Omnisens-iot/Estrategia-y-Gesti-n-de-Proyectos-para-Soluciones-IoT-/B_Investigacion/Gestion_de_proyectos/9. Crear matriz inicial de riesgos del proyecto.docx.pdf

## 9. Crear matriz inicial de riesgos del proyecto

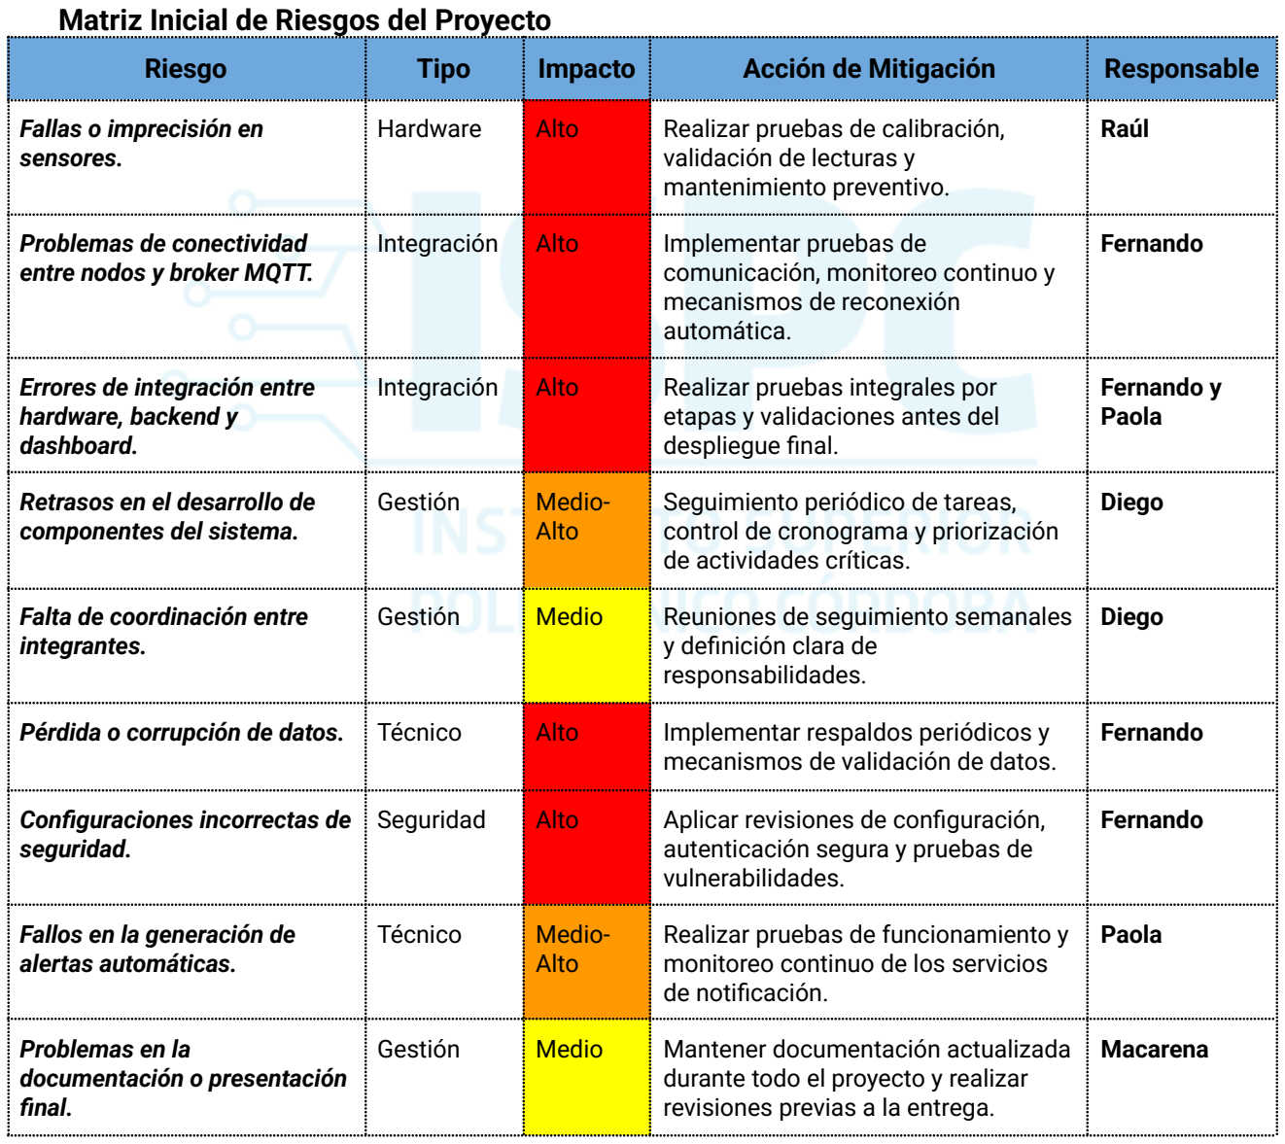
[picture p5: figure]
Matriz Inicial de Riesgos del Proyecto; Riesgo; Tipo; Impacto; Acción de Mitigación; Responsable; Fallas o imprecisión en sensores.; Hardware; Alto; Realizar pruebas de calibración,; validación de lecturas y mantenimiento preventivo.; Raúl; Problemas de conectividad entre nodos y broker MQTT.; Integración; Implementar pruebas de; comunicación, monitoreo continuo y mecanismos de reconexión automática.; Fernando; Errores de integración entre hardware, backend y dashboard.; Realizar pruebas integrales por; etapas y validaciones antes del despliegue final.; Fernando y Paola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

Pérdida o corrupción de datos. Técnico | Alto | Implementar respaldos periódicos y

### Resultado esperado

La matriz de riesgos permite identificar tempranamente posibles problemas técnicos y de gestión asociados al desarrollo de OmniSens. La asignación de responsables y acciones de mitigación facilita el seguimiento continuo de los riesgos y contribuye al cumplimiento de los objetivos del proyecto.
