Omnisens-iot/Estrategia-y-Gesti-n-de-Proyectos-para-Soluciones-IoT-/B_Investigacion/Modelo_negocios/6.1 Definir beneficios del sistema para el cliente.docx.pdf

### 6.1 Definir beneficios del sistema para el cliente

### 1. Mayor seguridad operativa

OmniSens permite monitorear variables ambientales críticas en tiempo real, facilitando la detección temprana de condiciones anómalas y mejorando la capacidad de respuesta ante posibles incidentes.

### 2. Reducción de riesgos

La generación automática de alertas y la supervisión continua ayudan a prevenir fallas operativas, minimizar interrupciones en los procesos y reducir la probabilidad de eventos que afecten la seguridad de las instalaciones.

### 3. Optimización de recursos

Al centralizar la información y automatizar tareas de monitoreo, se reducen los controles manuales, se mejora la eficiencia operativa y se facilita la toma de decisiones basada en datos confiables.

### 4. Cumplimiento normativo

El almacenamiento histórico de datos y la trazabilidad de la información permiten generar evidencias y reportes que contribuyen al cumplimiento de normativas de seguridad, higiene y control ambiental.

Resultado Final
OmniSens brinda a las organizaciones una herramienta que mejora la seguridad operativa, reduce riesgos, optimiza recursos y facilita el cumplimiento normativo, transformando datos ambientales en información útil para la toma de decisiones preventivas.
