Omnisens-iot/Estrategia-y-Gesti-n-de-Proyectos-para-Soluciones-IoT-/B_Investigacion/Gestion_de_proyectos/6. Definir roles y responsabilidades de los 5 integrantes.docx.pdf

6. Definir roles y responsabilidades de los 5 integrantes.
Integrante | Rol | Responsabilidades
Diego | Coordinador del Proyecto | Planificación y seguimiento de actividades, coordinación del equipo, control de cronograma, gestión de riesgos y supervisión general de los entregables.
Raúl | Responsable de Hardware y Firmware | Integración de sensores y nodos ESP32, desarrollo y mantenimiento del firmware, pruebas de funcionamiento y validación de la adquisición de datos.
Fernando | Responsable de Backend e Infraestructura | Configuración del broker MQTT, desarrollo de servicios backend, gestión de bases de datos, infraestructura cloud (AWS EC2), Docker y automatización de despliegues.
Paola | Responsable de Datos y Visualización | Diseño y desarrollo del dashboard, visualización de datos en tiempo real, configuración de alertas, reportes y validación de la calidad de los datos.
Macarena | Responsable de Documentación y Presentación | Elaboración de documentación técnica y funcional, actualización del repositorio, preparación de presentaciones, informes, defensa del proyecto y consolidación de entregables.

Resultado esperado

La definición de roles permite una distribución clara de responsabilidades dentro del equipo de OmniSens, favoreciendo la organización, la comunicación y el cumplimiento de los objetivos del proyecto, evitando superposiciones de tareas y optimizando el trabajo colaborativo.
