Omnisens-iot/Estrategia-y-Gesti-n-de-Proyectos-para-Soluciones-IoT-/B_Investigacion/Modelo_negocios/7.3 Analizar viabilidad en el mercado argentino.docx.pdf

### 7.3 Analizar viabilidad en el mercado argentino

Contexto económico
El contexto económico argentino presenta desafíos asociados a la inflación, la volatilidad cambiaria y las restricciones presupuestarias de muchas empresas. Sin embargo, estas condiciones también impulsan la búsqueda de soluciones que permitan optimizar recursos, reducir costos operativos y prevenir pérdidas derivadas de fallas o incidentes.

Capacidad de pago
Las PyMEs industriales suelen tener limitaciones para realizar grandes inversiones iniciales en tecnología. Por este motivo, el modelo SaaS de OmniSens resulta viable, ya que permite acceder a la solución mediante suscripciones escalables y costos predecibles, reduciendo la barrera de entrada.

Competencia
Existen soluciones de monitoreo industrial y plataformas IoT en el mercado, aunque muchas presentan costos elevados, requieren infraestructura compleja o están orientadas a grandes industrias. OmniSens busca diferenciarse mediante una propuesta accesible, escalable y adaptada a las necesidades de PyMEs, agroindustrias, empresas de energía, logística y plantas productivas.

Barreras identificadas

- Resistencia al cambio tecnológico y adopción de nuevas herramientas.
- Limitaciones presupuestarias para inversiones en transformación digital.
- Necesidad de capacitación para la utilización de plataformas de monitoreo.
- Competencia de proveedores tecnológicos consolidados en el sector industrial.

Resultado esperado

El análisis indica que OmniSens posee una viabilidad favorable en el mercado argentino, especialmente en sectores industriales que buscan mejorar la seguridad operativa, optimizar procesos y avanzar en su transformación digital. Su modelo SaaS, junto con una propuesta de valor basada en monitoreo en tiempo real y toma de decisiones preventivas, permite adaptarse a las necesidades y capacidades de inversión de las organizaciones objetivo.
