Omnisens-iot/Estrategia-y-Gesti-n-de-Proyectos-para-Soluciones-IoT-/B_Investigacion/Modelo_negocios/8.3 Evaluar riesgos del modelo de negocio.docx.pdf

### 8.3 Evaluar riesgos del modelo de negocio

Riesgo de adopción

Las empresas pueden mostrar resistencia inicial a incorporar nuevas tecnologías debido a costos percibidos, desconocimiento de soluciones IoT o preferencia por procesos tradicionales.

Impacto: Medio-Alto. Puede ralentizar la captación de clientes y la expansión comercial.

Riesgo económico

Variaciones en costos de hardware, infraestructura cloud, servicios de comunicación o condiciones macroeconómicas pueden afectar la rentabilidad del modelo SaaS.

Impacto: Alto. Puede generar desvíos presupuestarios y afectar la competitividad de la propuesta.

Riesgo tecnológico

Posibles fallas en sensores, conectividad, servicios cloud o integraciones entre componentes podrían afectar la disponibilidad y confiabilidad del sistema.

Impacto: Alto. La pérdida de datos o interrupción del monitoreo puede comprometer la confianza del cliente.

Riesgo de competencia

La presencia de proveedores consolidados de monitoreo industrial o la aparición de nuevas soluciones IoT puede reducir la participación de mercado de OmniSens.

Impacto: Medio. Requiere innovación continua y diferenciación basada en seguridad, integración y facilidad de implementación.

Resultado esperado

Se identifican como riesgos principales la adopción tecnológica por parte de los clientes, la variación de costos operativos, la disponibilidad tecnológica y la presión competitiva. Su gestión temprana permitirá fortalecer la viabilidad y sostenibilidad del modelo de negocio de OmniSens.
