Omnisens-iot/Estrategia-y-Gesti-n-de-Proyectos-para-Soluciones-IoT-/B_Investigacion/Modelo_negocios/2.3 Definir propuesta de valor.docx.pdf

### 2.3 Definir propuesta de valor por segmento

PyMEs Industriales

OmniSens permite centralizar variables ambientales críticas en una única plataforma, eliminando la dependencia de controles manuales y sensores aislados. La solución brinda monitoreo en tiempo real, alertas tempranas y trazabilidad de datos para mejorar la seguridad operativa y reducir riesgos.

Problema que resuelve: Ceguera operativa, registros manuales, falta de integración y detección tardía de incidentes.

Empresas de Energía, Agroindustria y Logística

OmniSens proporciona visibilidad continua sobre las condiciones ambientales y operativas de instalaciones distribuidas, facilitando la supervisión remota, la prevención de fallas y el cumplimiento de estándares de seguridad.

Problema que resuelve: Falta de monitoreo centralizado, riesgos operativos y dificultades para supervisar múltiples ubicaciones.

Organismos de Control y Gestión Industrial

OmniSens permite acceder a información ambiental confiable, histórica y en tiempo real para apoyar auditorías, controles y procesos de cumplimiento normativo relacionados con seguridad e impacto ambiental.

Problema que resuelve: Escasa disponibilidad de información centralizada para el control, seguimiento y verificación de condiciones operativas.

Resultado esperado

OmniSens ofrece una propuesta de valor basada en la integración de datos ambientales, el monitoreo continuo y la generación de alertas tempranas, permitiendo transformar información en decisiones preventivas que mejoran la seguridad, reducen riesgos y optimizan la operación industrial.
