Omnisens-iot/Estrategia-y-Gesti-n-de-Proyectos-para-Soluciones-IoT-/B_Investigacion/Seguridad_IoT/Análisis de Vulnerabilidades y Seguridad del Código Fuente en OmniSens Industrial Suite.pdf

## Título

Análisis de Vulnerabilidades y Seguridad del Código Fuente en OmniSens Industrial Suite

# Introducción

La seguridad del software constituye un aspecto fundamental dentro del desarrollo de sistemas IoT industriales. Los errores de programación, dependencias vulnerables y malas prácticas de desarrollo pueden generar riesgos que afecten la confidencialidad, integridad y disponibilidad de los servicios.

Con el objetivo de fortalecer la seguridad de OmniSens Industrial Suite, se incorporan prácticas de análisis estático de código y revisión continua de vulnerabilidades durante el ciclo de desarrollo. Estas actividades permiten identificar problemas de seguridad de forma temprana y reducir la probabilidad de incidentes en producción.

La estrategia se basa en la utilización de herramientas de análisis automatizado, revisión de firmware, control de dependencias y aplicación de buenas prácticas de desarrollo seguro.

# Objetivo

Detectar vulnerabilidades y fallas de seguridad en el código fuente del proyecto OmniSens Industrial Suite mediante mecanismos de análisis automatizado y revisión continua.

# Activación de Code Scanning en GitHub

GitHub proporciona herramientas de análisis de seguridad que permiten examinar automáticamente el código fuente del proyecto.

Entre las capacidades más importantes se encuentran:

- Identificación de vulnerabilidades conocidas.
- Detección de malas prácticas de programación.
- Revisión continua mediante integración con el repositorio.
- Alertas automáticas ante problemas detectados.
- Seguimiento histórico de vulnerabilidades.

La incorporación de Code Scanning permite integrar la seguridad directamente dentro del flujo de trabajo del proyecto.

# Análisis del Firmware ESP32

Los nodos Edge basados en ESP32 constituyen componentes críticos de la arquitectura OmniSens.

Durante la revisión del firmware se consideran aspectos como:

- Manejo seguro de memoria.
- Validación de entradas provenientes de sensores.
- Protección frente a desbordamientos de memoria.
- Control adecuado de errores.
- Gestión segura de comunicaciones.

La revisión del firmware contribuye a reducir riesgos asociados a dispositivos embebidos que operan en entornos industriales.

# Revisión de Dependencias

Los proyectos modernos utilizan múltiples bibliotecas y componentes de terceros.

La revisión de dependencias tiene como objetivo:

- Detectar versiones vulnerables.
- Identificar componentes obsoletos.
- Evaluar riesgos asociados a software externo.
- Mantener actualizadas las librerías utilizadas.

Esta práctica reduce la exposición a vulnerabilidades conocidas que podrían afectar al sistema.

# Corrección de Vulnerabilidades

Una vez identificadas posibles vulnerabilidades, se aplican medidas correctivas que incluyen:

- Actualización de bibliotecas.

- Corrección de errores de programación.
- Refactorización de componentes inseguros.
- Eliminación de configuraciones inseguras.
- Aplicación de buenas prácticas de desarrollo seguro.

La corrección temprana de vulnerabilidades disminuye significativamente los riesgos operativos y de ciberseguridad.

# Beneficios para OmniSens

La implementación de análisis continuo de seguridad aporta múltiples ventajas:

- Mayor calidad del software.
- Reducción de riesgos de explotación.
- Detección temprana de errores.
- Incremento de la confiabilidad del sistema.
- Mejora del mantenimiento del proyecto.
- Cumplimiento de buenas prácticas de DevSecOps.

# Relación con la Arquitectura del Proyecto

La seguridad del código impacta directamente sobre todos los componentes de OmniSens:

- Firmware ESP32.
- Comunicaciones MQTT.
- Servicios Docker.
- Node-RED.
- MariaDB.
- Interfaces de monitoreo.

Por este motivo, la revisión continua del software se considera una medida transversal a toda la plataforma.

# Resultado Esperado

La aplicación de herramientas de análisis de código, revisión de firmware y control de dependencias permite disponer de una base de software más robusta, confiable y resistente frente a amenazas de seguridad.

# Conclusión

La seguridad del software debe abordarse desde las primeras etapas del desarrollo. La incorporación de mecanismos de análisis automático y revisión continua permite detectar vulnerabilidades antes de que afecten a la operación del sistema.

En OmniSens Industrial Suite estas prácticas contribuyen a construir una plataforma más segura, alineada con los principios de Seguridad desde el Diseño y las recomendaciones de la Industria 4.0.
