Omnisens-iot/Estrategia-y-Gesti-n-de-Proyectos-para-Soluciones-IoT-/B_Investigacion/Seguridad_IoT/Rotación de Credenciales y Gestión de Tokens en OmniSens Industrial Suite.pdf

# Rotación de Credenciales y Gestión de Tokens en OmniSens Industrial Suite

## Introducción

La gestión segura de credenciales constituye uno de los pilares fundamentales de la ciberseguridad moderna. En los sistemas IoT industriales, las credenciales permiten autenticar dispositivos, usuarios y servicios que participan en el intercambio de información crítica.

La exposición accidental de claves, contraseñas o tokens puede comprometer la confidencialidad de los datos, permitir accesos no autorizados y afectar la operación del sistema. Por este motivo, OmniSens Industrial Suite incorpora una estrategia de rotación de credenciales que reduce el impacto potencial de una filtración y fortalece la seguridad general de la plataforma.

El presente documento describe las políticas, mecanismos y procedimientos definidos para la renovación periódica de credenciales y tokens utilizados dentro de la arquitectura del proyecto.

# Objetivo

Reducir los riesgos asociados a la exposición de credenciales mediante la implementación de políticas de rotación, renovación periódica de tokens y automatización de procesos de gestión de acceso.

# Importancia de la Rotación de Credenciales

Las credenciales representan la identidad digital de los componentes del sistema. Si una clave es comprometida y permanece activa durante largos períodos de tiempo, un atacante podría mantener acceso no autorizado sin ser detectado.

La rotación periódica permite:

- Limitar la vida útil de las credenciales.
- Reducir el impacto de filtraciones.
- Disminuir la superficie de ataque.
- Cumplir buenas prácticas de seguridad.
- Mejorar la trazabilidad de accesos.

# Política de Rotación Definida

Para OmniSens se establece una política basada en los siguientes principios:

## Principio de Mínimo Privilegio

Cada usuario, dispositivo o servicio debe disponer únicamente de los permisos necesarios para realizar sus funciones.

## Renovación Periódica

Las credenciales deben ser reemplazadas regularmente según el nivel de criticidad del recurso protegido.

## Revocación Inmediata

Las credenciales comprometidas deben ser deshabilitadas y reemplazadas de forma inmediata.

## Gestión Centralizada

Las claves y tokens deben administrarse mediante procedimientos documentados y controlados.

# Renovación de Tokens

Los tokens utilizados para autenticación de servicios y APIs deben poseer una vigencia limitada.

La estrategia contempla:

- Generación de tokens temporales.
- Fecha de expiración definida.
- Renovación automática antes del vencimiento.
- Revocación de tokens comprometidos.
- Registro de eventos relacionados con autenticación.

Esta práctica reduce significativamente el riesgo asociado a credenciales robadas o expuestas.

# Automatización de Cambios

Con el fin de minimizar errores humanos y mejorar la eficiencia operativa, la renovación de credenciales debe automatizarse siempre que sea posible.

Las acciones recomendadas incluyen:

- Generación automática de tokens.
- Renovación programada de credenciales.
- Actualización segura de configuraciones.
- Registro automático de cambios.
- Notificaciones ante vencimientos próximos.

La automatización permite garantizar consistencia y reducir tareas manuales repetitivas.

# Aplicación en la Arquitectura OmniSens

Dentro de la arquitectura propuesta, la política de rotación puede aplicarse sobre:

## Broker MQTT

- Renovación de credenciales de acceso.
- Actualización periódica de certificados.

## API del Sistema

- Tokens de autenticación con expiración.
- Renovación automática mediante mecanismos seguros.

## Base de Datos

- Actualización periódica de contraseñas administrativas.
- Restricción de privilegios según rol.

## Servicios Docker

- Gestión segura de variables de entorno.
- Eliminación de credenciales embebidas en imágenes.

## Repositorio GitHub

- Protección de secretos.
- Eliminación de claves expuestas.

- Uso de variables seguras para despliegues.

# Beneficios para la Seguridad

La implementación de una estrategia de rotación de credenciales aporta múltiples beneficios:

- Disminución del riesgo de accesos no autorizados.
- Reducción del impacto de filtraciones.
- Mayor control sobre usuarios y dispositivos.
- Cumplimiento de buenas prácticas de ciberseguridad.
- Incremento de la resiliencia del sistema.

# Procedimiento Documentado

Ante la detección de una posible exposición de credenciales se deberá:

1. Identificar la credencial comprometida.
2. Revocar inmediatamente su validez.
3. Generar una nueva credencial.
4. Actualizar las configuraciones afectadas.
5. Verificar el correcto funcionamiento del servicio.
6. Registrar el incidente y las acciones realizadas.

Este procedimiento permite responder rápidamente ante eventos de seguridad.

# Resultado Esperado

La aplicación de políticas de rotación y renovación de credenciales permite disponer de un sistema con credenciales dinámicas, reduciendo significativamente los riesgos asociados a accesos no autorizados y fortaleciendo la seguridad integral de OmniSens Industrial Suite.

# Conclusión

La rotación periódica de credenciales constituye una medida esencial dentro de cualquier estrategia de ciberseguridad moderna. Su implementación en OmniSens Industrial Suite contribuye a proteger la infraestructura, los servicios y los datos del sistema, disminuyendo el impacto potencial de incidentes relacionados con la exposición de claves o tokens.

La combinación de renovación periódica, automatización y procedimientos documentados fortalece la confiabilidad de la plataforma y mejora su capacidad de respuesta ante amenazas de seguridad.
