Omnisens-iot/Estrategia-y-Gesti-n-de-Proyectos-para-Soluciones-IoT-/B_Investigacion/Gestion_de_proyectos/Kpys.jpg

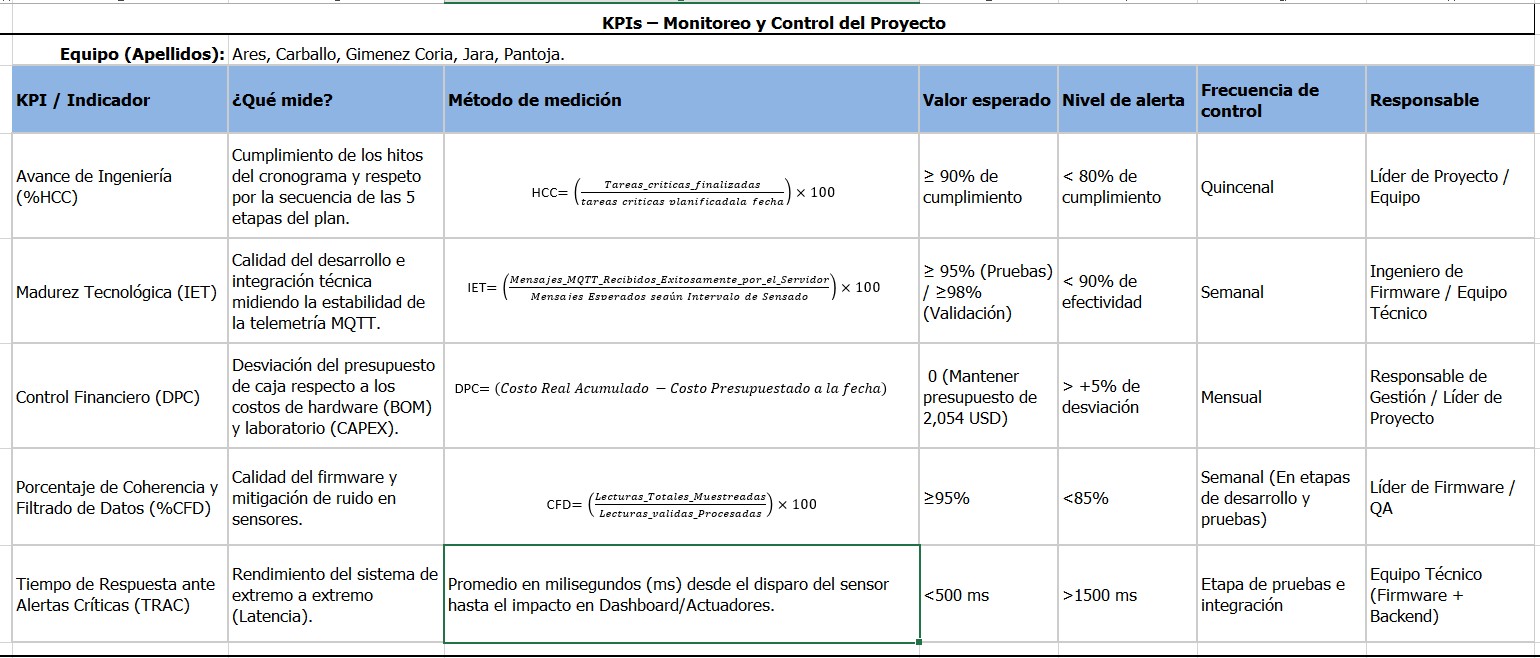
B_Investigacion/Gestion_de_proyectos/Kpys.jpg
