Omnisens-iot/Estrategia-y-Gesti-n-de-Proyectos-para-Soluciones-IoT-/B_Investigacion/Modelo_negocios/BMCOmnisens.png

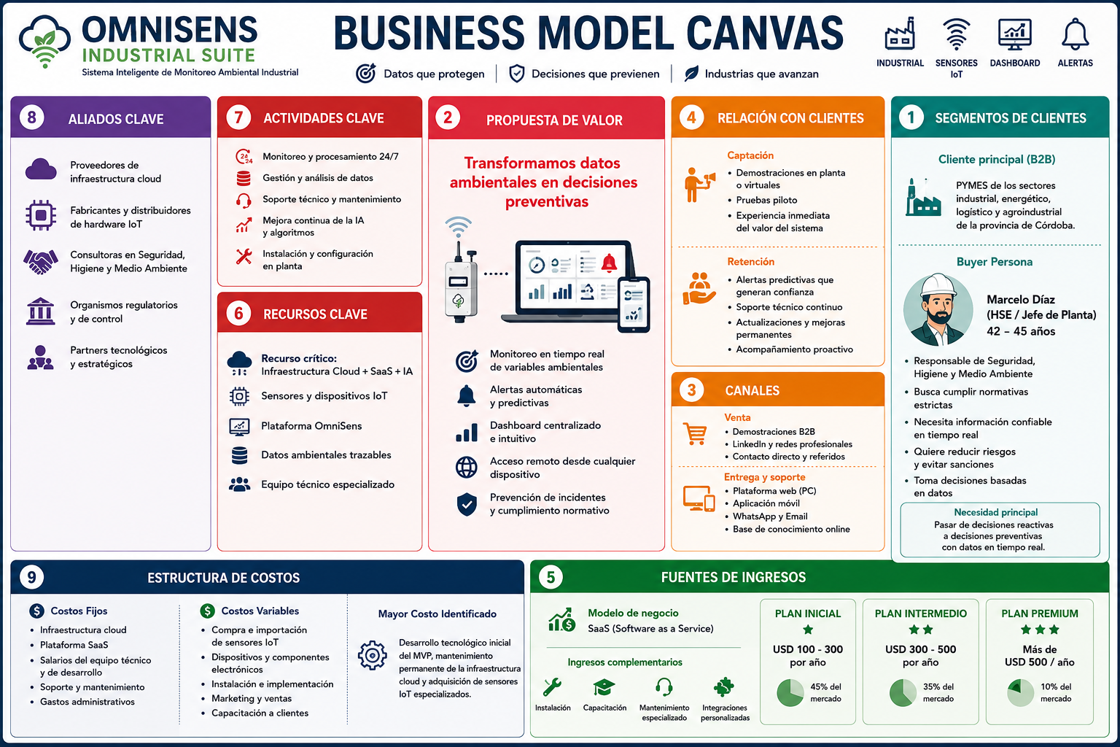
B_Investigacion/Modelo_negocios/BMCOmnisens.png
