Omnisens-iot/Estrategia-y-Gesti-n-de-Proyectos-para-Soluciones-IoT-/B_Investigacion/Modelo_negocios/Lienzo Paso 1.jpeg

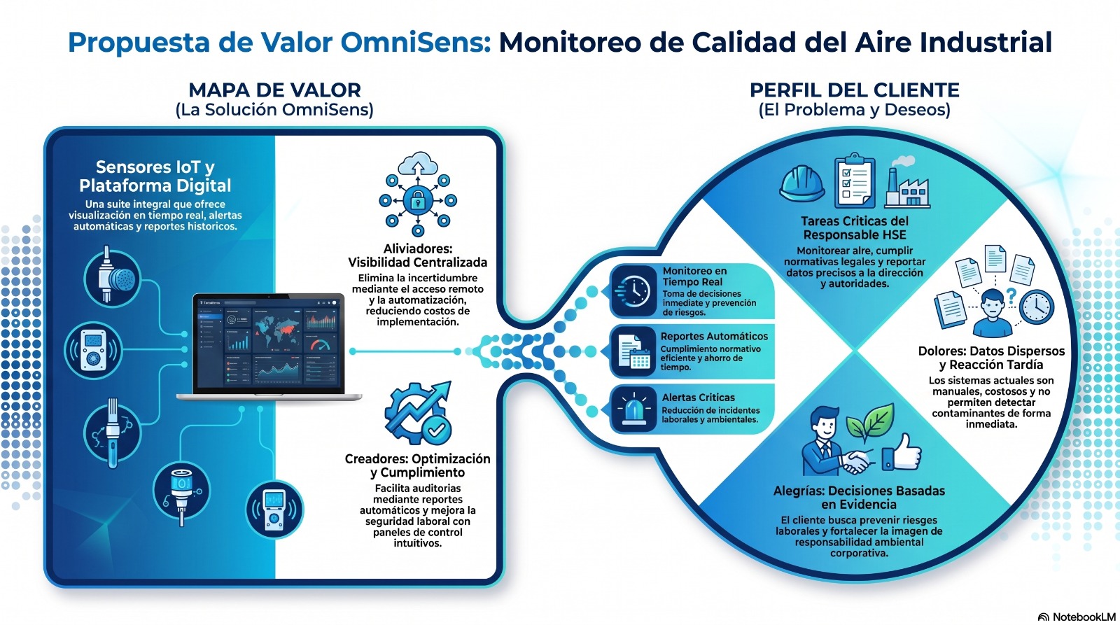
B_Investigacion/Modelo_negocios/Lienzo Paso 1.jpeg
