Omnisens-iot/Estrategia-y-Gesti-n-de-Proyectos-para-Soluciones-IoT-/C_Prototipos/OmniSens/Dispositivos/Modelos 3D/chasis_2_0/corte_modelo.png

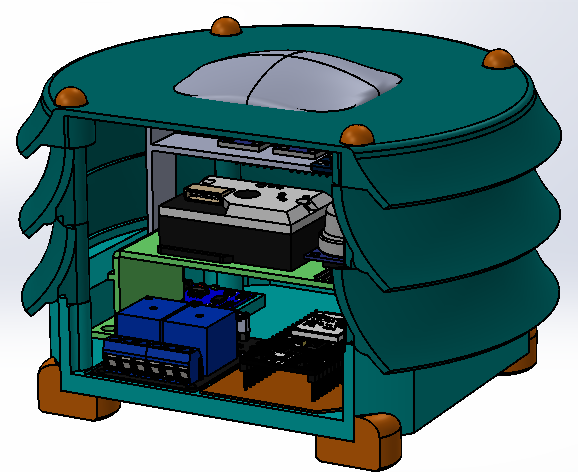
C_Prototipos/OmniSens/Dispositivos/Modelos 3D/chasis_2_0/corte_modelo.png
