Omnisens-iot/Estrategia-y-Gesti-n-de-Proyectos-para-Soluciones-IoT-/C_Prototipos/OmniSens/frontend/src/assets/titulo_omni.png

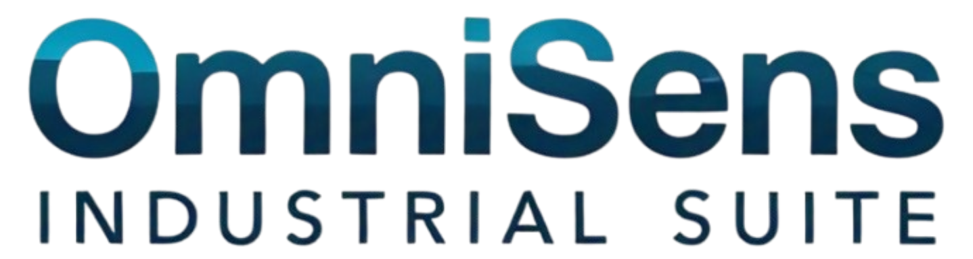
C_Prototipos/OmniSens/frontend/src/assets/titulo_omni.png
