Omnisens-iot/Estrategia-y-Gesti-n-de-Proyectos-para-Soluciones-IoT-/C_Prototipos/OmniSens/Dispositivos/Modelos 3D/tiraLedWS2812.SLDPRT

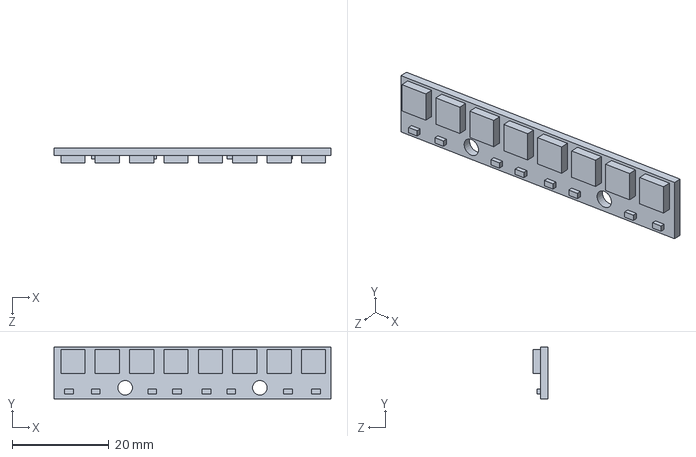
[picture p35: CAD file, 2026-04-17]
C_Prototipos/OmniSens/Dispositivos/Modelos 3D/tiraLedWS2812.SLDPRT
57.2 x 10.7 x 3.00 mm
