Omnisens-iot/Estrategia-y-Gesti-n-de-Proyectos-para-Soluciones-IoT-/C_Prototipos/OmniSens/Dispositivos/Modelos 3D/chasis_2_0/sensores/tapa_dust_chim.SLDPRT

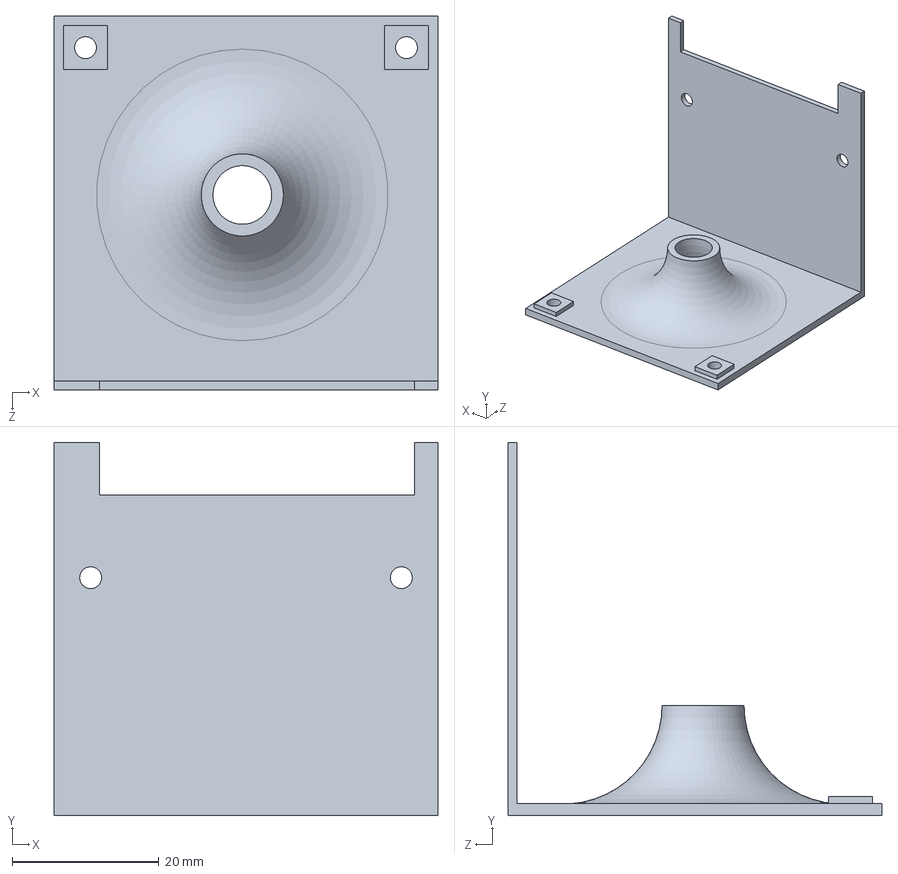
[picture p36: CAD file, 2026-06-27]
C_Prototipos/OmniSens/Dispositivos/Modelos 3D/chasis_2_0/sensores/tapa_dust_chim.SLDPRT
52.4 x 50.9 x 51.0 mm
