Omnisens-iot/Estrategia-y-Gesti-n-de-Proyectos-para-Soluciones-IoT-/C_Prototipos/OmniSens/Dispositivos/Modelos 3D/modulo_LoRa.SLDPRT

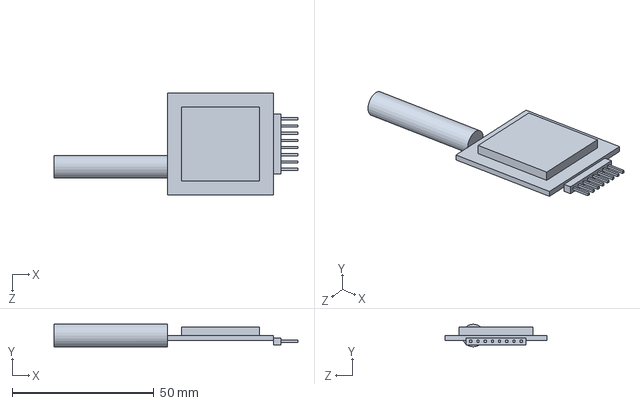
[picture p37: CAD file, 2026-04-17]
C_Prototipos/OmniSens/Dispositivos/Modelos 3D/modulo_LoRa.SLDPRT
86.1 x 8.00 x 36.0 mm
