Omnisens-iot/Estrategia-y-Gesti-n-de-Proyectos-para-Soluciones-IoT-/C_Prototipos/OmniSens/Dispositivos/Modelos 3D/chasis_2_0/sensores/base_sens.SLDPRT

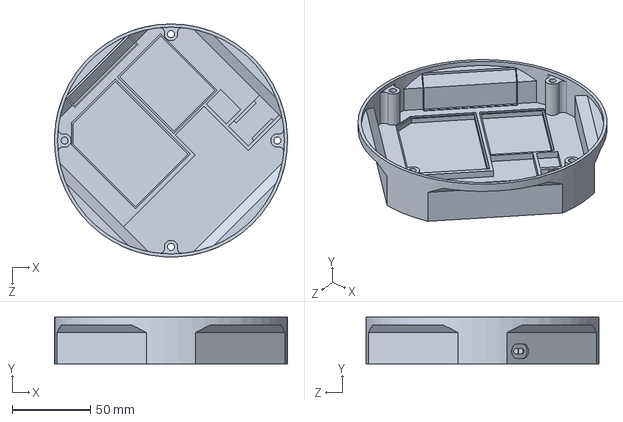
[picture p38: CAD file, 2026-06-15]
C_Prototipos/OmniSens/Dispositivos/Modelos 3D/chasis_2_0/sensores/base_sens.SLDPRT
148.9 x 30.0 x 149.0 mm
