Omnisens-iot/Estrategia-y-Gesti-n-de-Proyectos-para-Soluciones-IoT-/C_Prototipos/OmniSens/Dispositivos/Modelos 3D/chasis_2_0/sensores/pata.SLDPRT

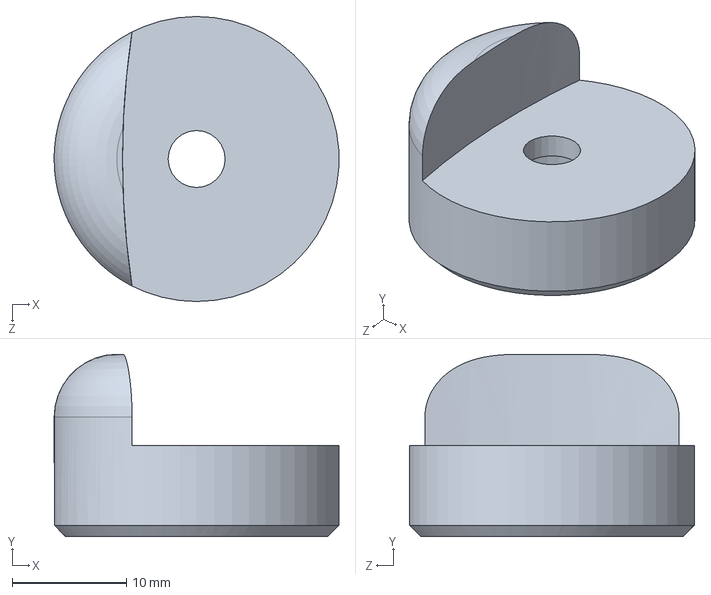
[picture p39: CAD file, 2026-06-15]
C_Prototipos/OmniSens/Dispositivos/Modelos 3D/chasis_2_0/sensores/pata.SLDPRT
25.0 x 16.0 x 25.0 mm
