Omnisens-iot/Estrategia-y-Gesti-n-de-Proyectos-para-Soluciones-IoT-/C_Prototipos/OmniSens/Dispositivos/Modelos 3D/modulo_porta_componente.SLDPRT

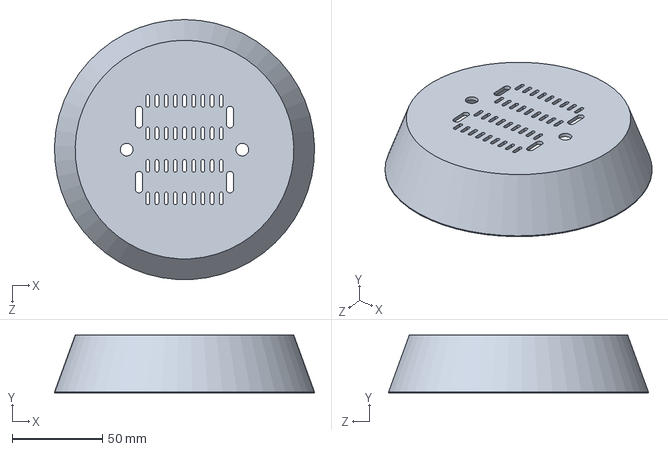
[picture p40: CAD file, 2026-04-17]
C_Prototipos/OmniSens/Dispositivos/Modelos 3D/modulo_porta_componente.SLDPRT
143.8 x 32.0 x 143.8 mm
