Omnisens-iot/Estrategia-y-Gesti-n-de-Proyectos-para-Soluciones-IoT-/C_Prototipos/OmniSens/Dispositivos/Modelos 3D/chasis_2_0/sensores/techo_sensores.SLDPRT

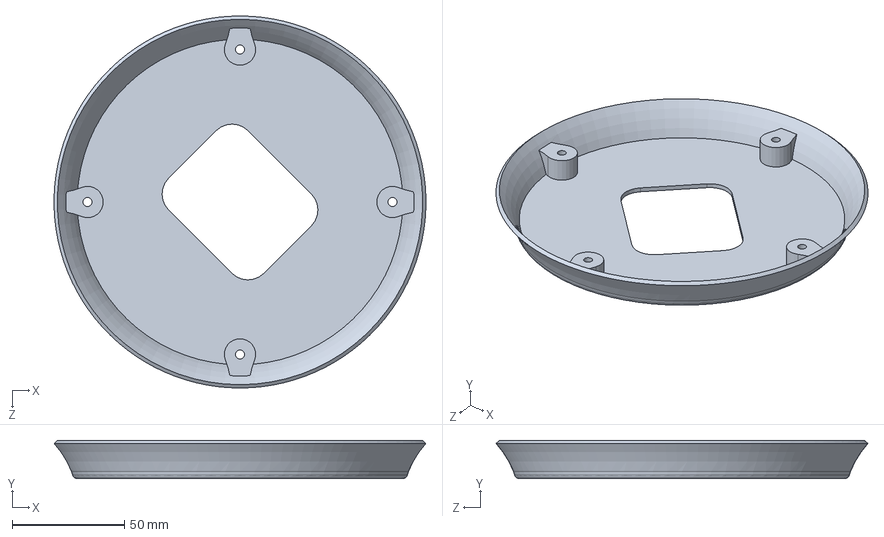
[picture p41: CAD file, 2026-06-15]
C_Prototipos/OmniSens/Dispositivos/Modelos 3D/chasis_2_0/sensores/techo_sensores.SLDPRT
165.8 x 17.0 x 165.9 mm
