Omnisens-iot/Estrategia-y-Gesti-n-de-Proyectos-para-Soluciones-IoT-/C_Prototipos/OmniSens/Dispositivos/Modelos 3D/chasis_2_0/sensores/espacio de componentes.SLDPRT

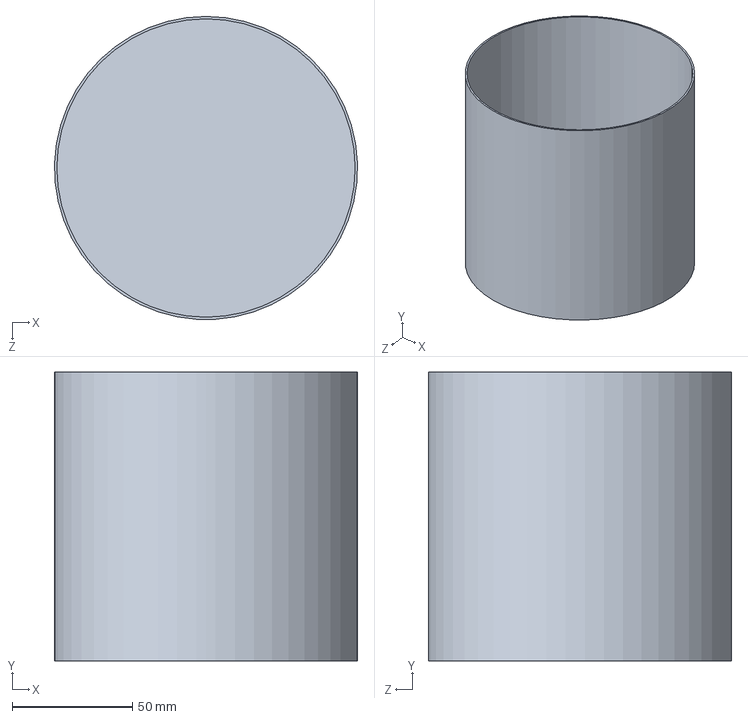
[picture p42: CAD file, 2026-06-15]
C_Prototipos/OmniSens/Dispositivos/Modelos 3D/chasis_2_0/sensores/espacio de componentes.SLDPRT
125.9 x 120.0 x 126.0 mm
