Omnisens-iot/Estrategia-y-Gesti-n-de-Proyectos-para-Soluciones-IoT-/C_Prototipos/OmniSens/Dispositivos/Modelos 3D/sensor LDR.SLDPRT

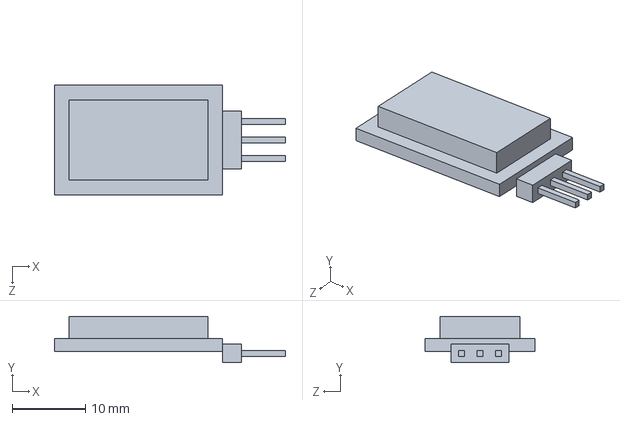
[picture p43: CAD file, 2026-04-17]
C_Prototipos/OmniSens/Dispositivos/Modelos 3D/sensor LDR.SLDPRT
31.6 x 6.34 x 15.0 mm
