Omnisens-iot/Estrategia-y-Gesti-n-de-Proyectos-para-Soluciones-IoT-/C_Prototipos/OmniSens/Dispositivos/Modelos 3D/base_baliza_LDR_LoRa.SLDPRT

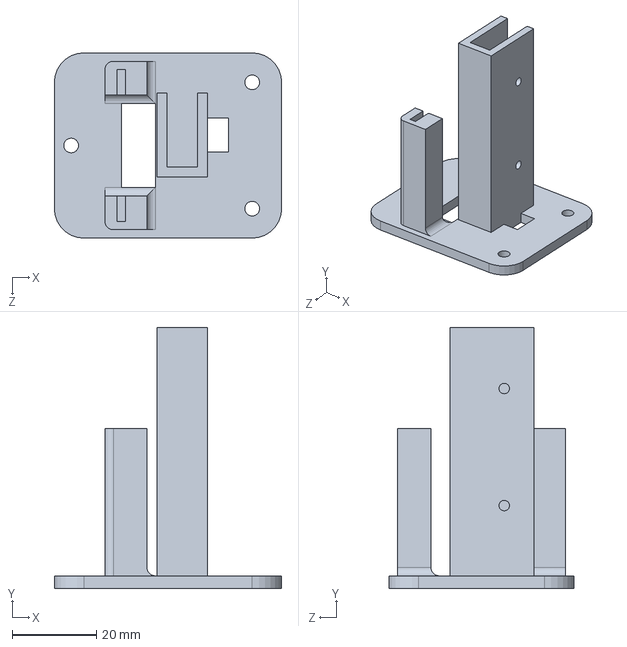
[picture p44: CAD file, 2026-04-17]
C_Prototipos/OmniSens/Dispositivos/Modelos 3D/base_baliza_LDR_LoRa.SLDPRT
54.0 x 62.0 x 44.0 mm
