Omnisens-iot/Estrategia-y-Gesti-n-de-Proyectos-para-Soluciones-IoT-/C_Prototipos/OmniSens/Dispositivos/Modelos 3D/chasis_2_0/sensores/ventana.SLDPRT

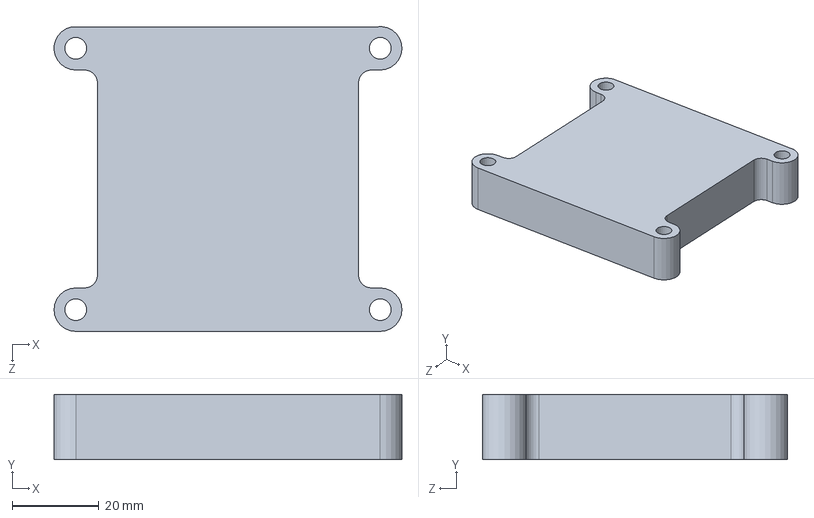
[picture p45: CAD file, 2026-06-15]
C_Prototipos/OmniSens/Dispositivos/Modelos 3D/chasis_2_0/sensores/ventana.SLDPRT
80.0 x 15.0 x 70.1 mm
