Omnisens-iot/Estrategia-y-Gesti-n-de-Proyectos-para-Soluciones-IoT-/C_Prototipos/OmniSens/Dispositivos/Modelos 3D/Tapa_superior_con_ventana.sldprt

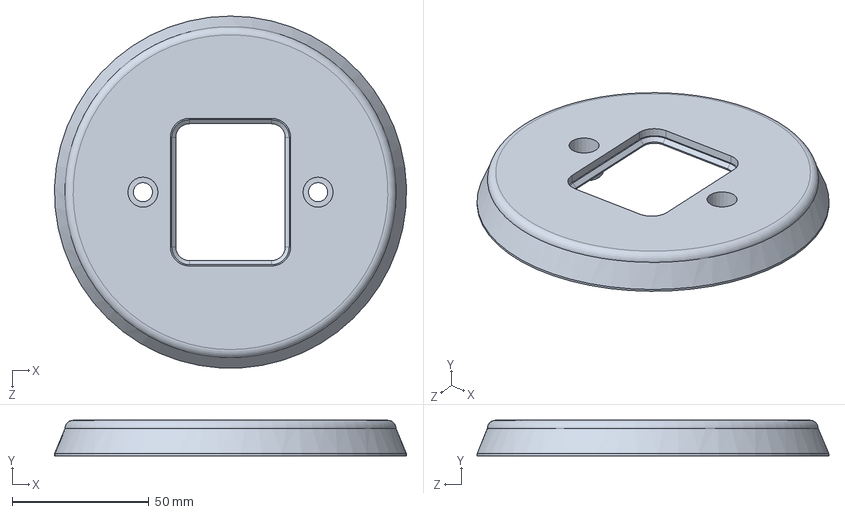
[picture p47: CAD file, 2026-04-17]
C_Prototipos/OmniSens/Dispositivos/Modelos 3D/Tapa_superior_con_ventana.sldprt
128.6 x 13.0 x 128.6 mm
