Omnisens-iot/Estrategia-y-Gesti-n-de-Proyectos-para-Soluciones-IoT-/C_Prototipos/OmniSens/Dispositivos/Modelos 3D/separador_cuerpos.SLDPRT

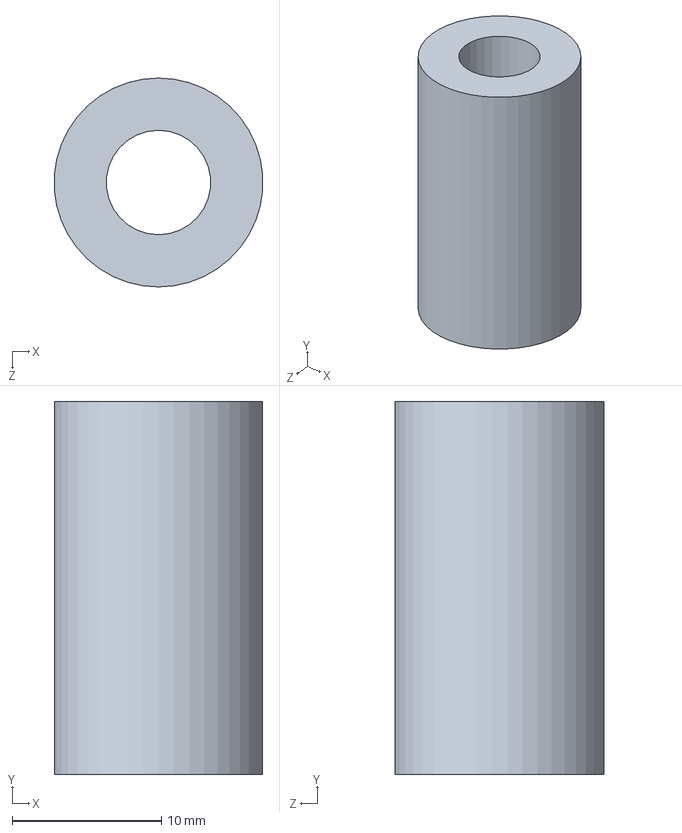
[picture p49: CAD file, 2026-04-17]
C_Prototipos/OmniSens/Dispositivos/Modelos 3D/separador_cuerpos.SLDPRT
14.0 x 25.0 x 14.0 mm
