Omnisens-iot/Estrategia-y-Gesti-n-de-Proyectos-para-Soluciones-IoT-/C_Prototipos/OmniSens/Dispositivos/Modelos 3D/chasis_2_0/sensores/mypushbutton.stp

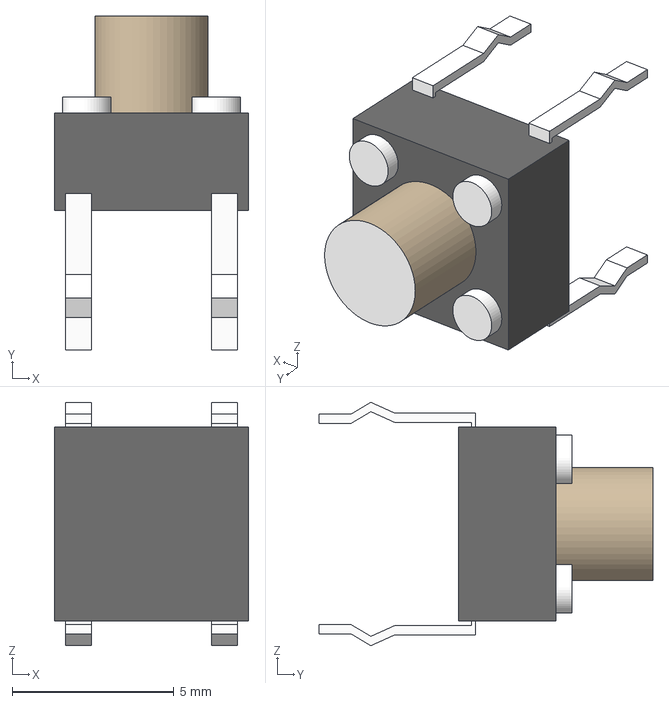
[picture p51: CAD file, 2026-06-13]
C_Prototipos/OmniSens/Dispositivos/Modelos 3D/chasis_2_0/sensores/mypushbutton.stp
6.00 x 10.3 x 7.52 mm
