Omnisens-iot/Estrategia-y-Gesti-n-de-Proyectos-para-Soluciones-IoT-/C_Prototipos/OmniSens/Dispositivos/Modelos 3D/chasis_2_0/sensores/HernanMH_Led 3mm Verde_.step

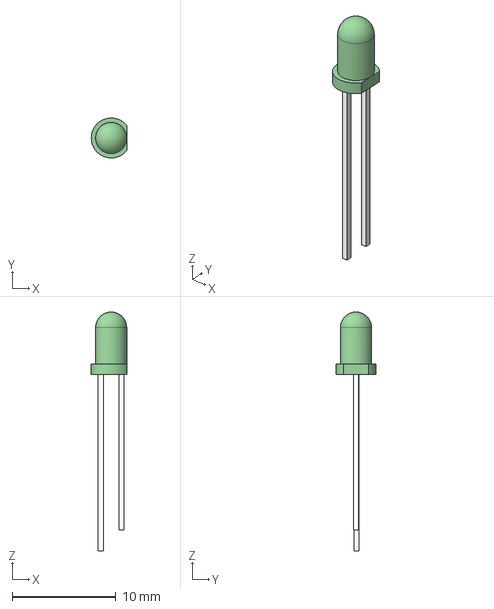
[picture p52: CAD file, 2026-06-13]
C_Prototipos/OmniSens/Dispositivos/Modelos 3D/chasis_2_0/sensores/HernanMH_Led 3mm Verde_.step
3.42 x 3.85 x 23.0 mm
