Omnisens-iot/Estrategia-y-Gesti-n-de-Proyectos-para-Soluciones-IoT-/C_Prototipos/OmniSens/Dispositivos/Modelos 3D/chasis_2_0/sensores/Dust sensor GP2Y1010AU0F.step

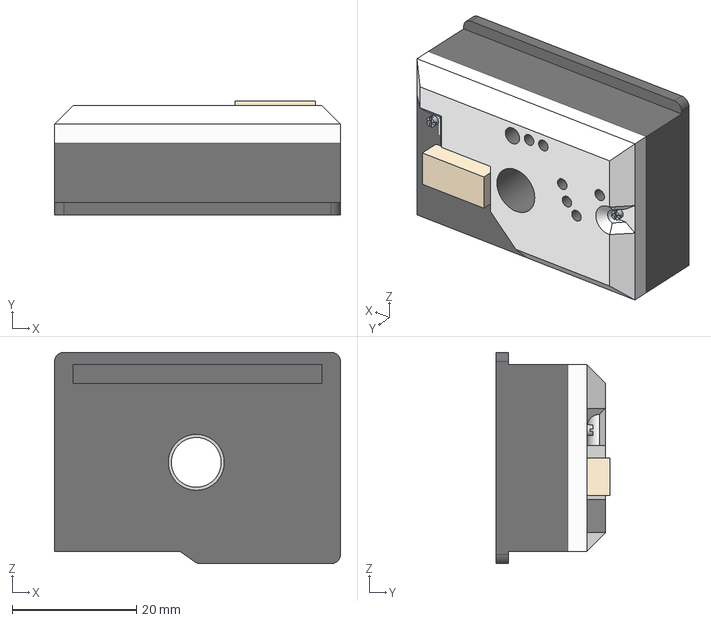
[picture p53: CAD file, 2026-06-13]
C_Prototipos/OmniSens/Dispositivos/Modelos 3D/chasis_2_0/sensores/Dust sensor GP2Y1010AU0F.step
46.0 x 18.3 x 34.0 mm
