Omnisens-iot/Estrategia-y-Gesti-n-de-Proyectos-para-Soluciones-IoT-/C_Prototipos/OmniSens/Dispositivos/Modelos 3D/chasis_2_0/sensores/soporte_controlador.SLDPRT

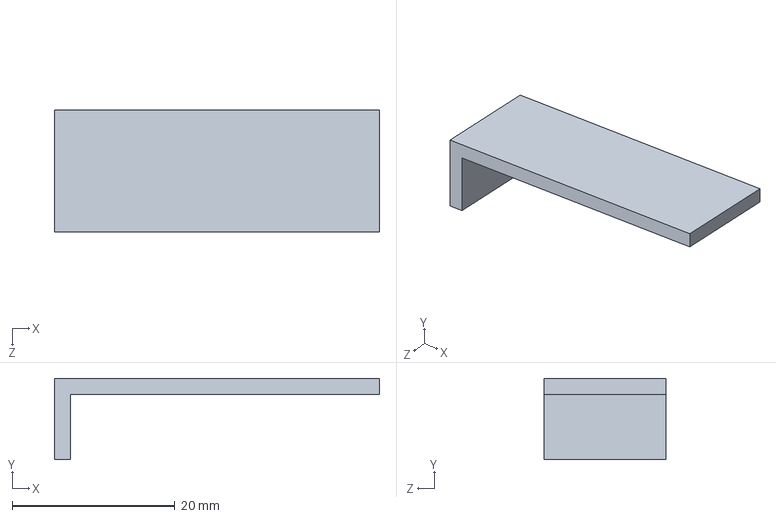
[picture p54: CAD file, 2026-06-13]
C_Prototipos/OmniSens/Dispositivos/Modelos 3D/chasis_2_0/sensores/soporte_controlador.SLDPRT
40.0 x 10.0 x 15.0 mm
