Omnisens-iot/Estrategia-y-Gesti-n-de-Proyectos-para-Soluciones-IoT-/C_Prototipos/OmniSens/Dispositivos/Modelos 3D/chasis_2_0/sensores/MQ135_sensor.step

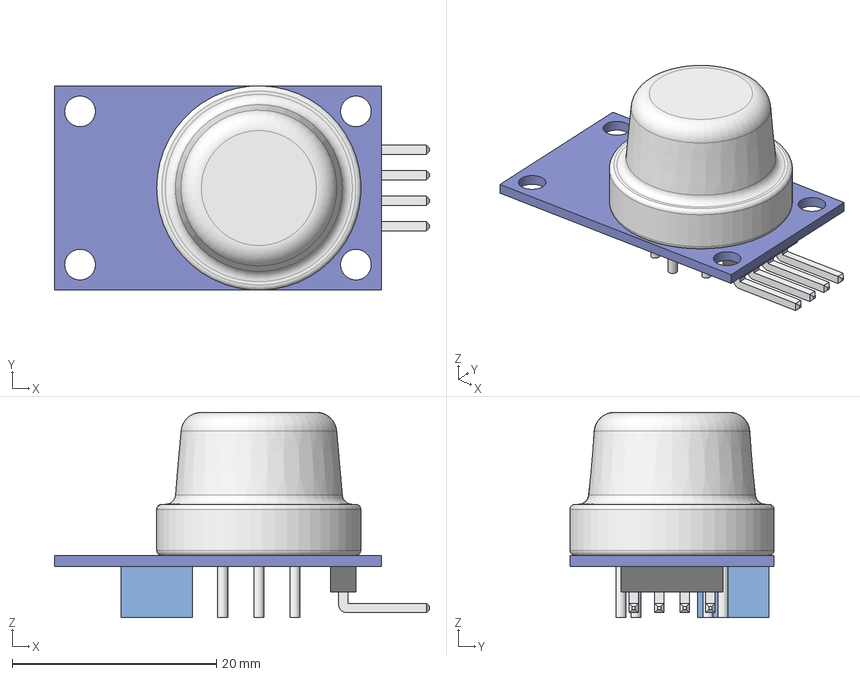
[picture p55: CAD file, 2026-06-13]
C_Prototipos/OmniSens/Dispositivos/Modelos 3D/chasis_2_0/sensores/MQ135_sensor.step
36.7 x 20.0 x 20.1 mm
