Omnisens-iot/Estrategia-y-Gesti-n-de-Proyectos-para-Soluciones-IoT-/C_Prototipos/OmniSens/Dispositivos/Modelos 3D/chasis_2_0/sensores/1S 4056 BMS USB C Module 01b.step

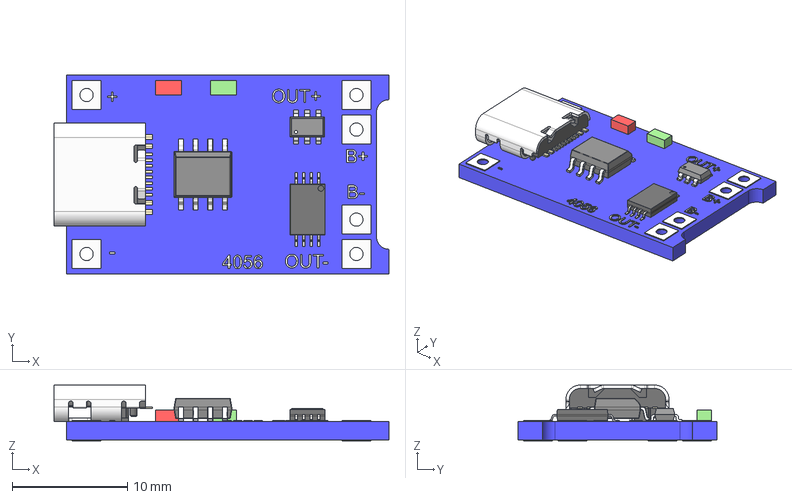
[picture p60: CAD file, 2026-06-13]
C_Prototipos/OmniSens/Dispositivos/Modelos 3D/chasis_2_0/sensores/1S 4056 BMS USB C Module 01b.step
29.1 x 17.3 x 4.86 mm
Shroud
Plastic Body & Connector
ATiny45_Body
ATiny45_Pin x 8
IC SMD 8 Pins
Pin2
Pin4
Pin6
Pin1
Pin3
Pin5
