Omnisens-iot/Estrategia-y-Gesti-n-de-Proyectos-para-Soluciones-IoT-/C_Prototipos/OmniSens/Dispositivos/Modelos 3D/chasis_2_0/sensores/100mill Male Pin Header_5P_R.STEP

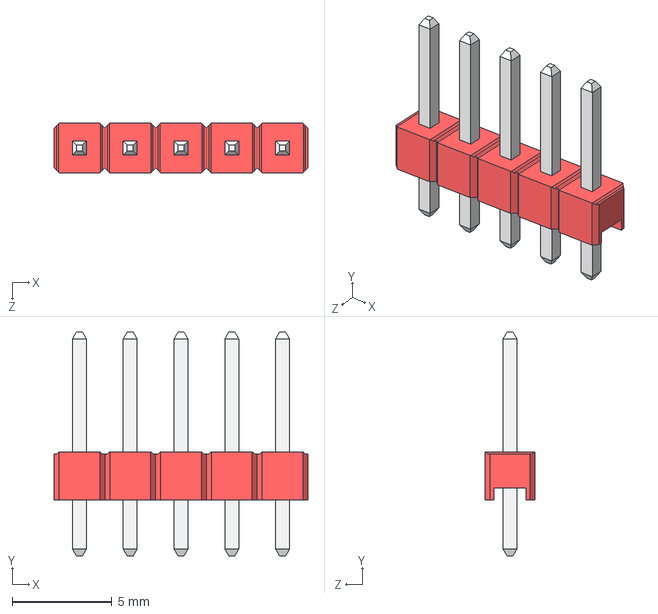
[picture p62: CAD file, 2026-06-13]
C_Prototipos/OmniSens/Dispositivos/Modelos 3D/chasis_2_0/sensores/100mill Male Pin Header_5P_R.STEP
12.7 x 11.2 x 2.50 mm
